butterstick-fpga/butterstick-hardware/documentation/images/800px/butterstick_r1d0_001.jpg

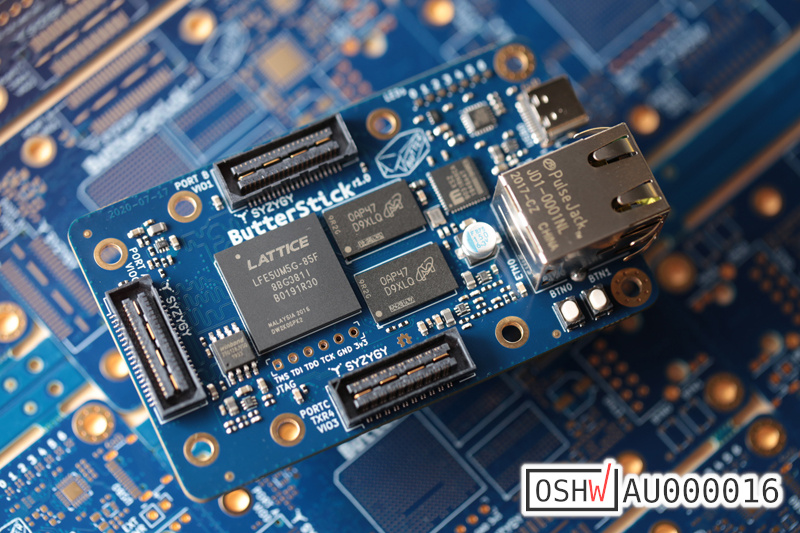
documentation/images/800px/butterstick_r1d0_001.jpg
