butterstick-fpga/butterstick-hardware/documentation/images/butterstick_render_r1d0.png

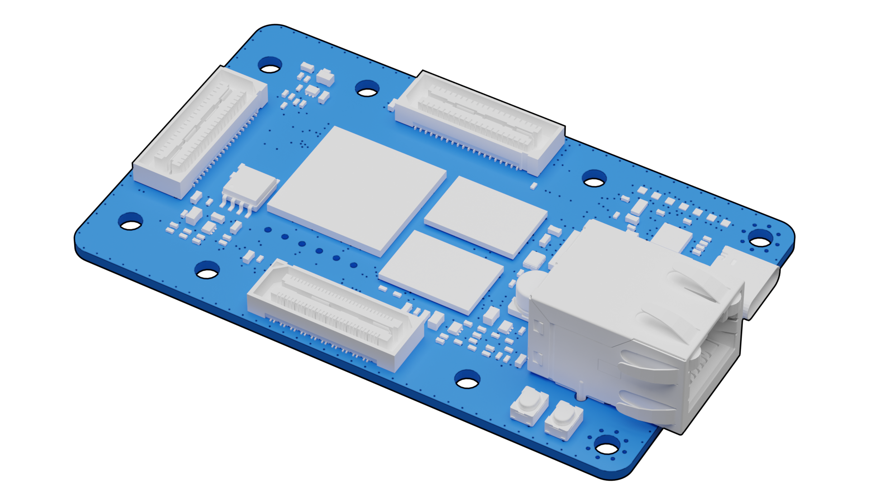
documentation/images/butterstick_render_r1d0.png
