butterstick-fpga/butterstick-hardware/documentation/repository-open-graph-template.png

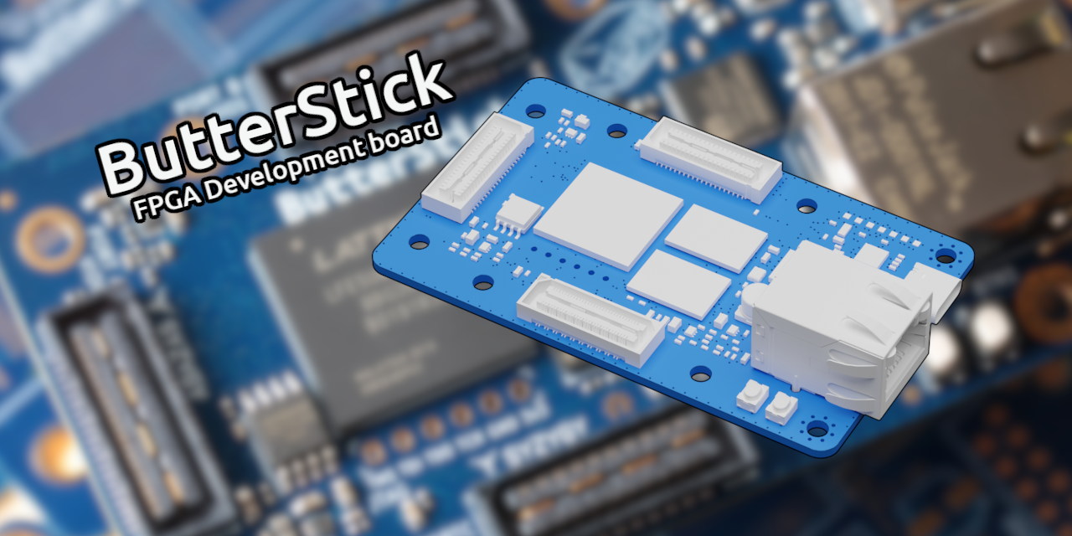
documentation/repository-open-graph-template.png
