butterstick-fpga/butterstick-hardware/hardware/ButterStick_r0.2/output/plot/ButterStick-Back.png

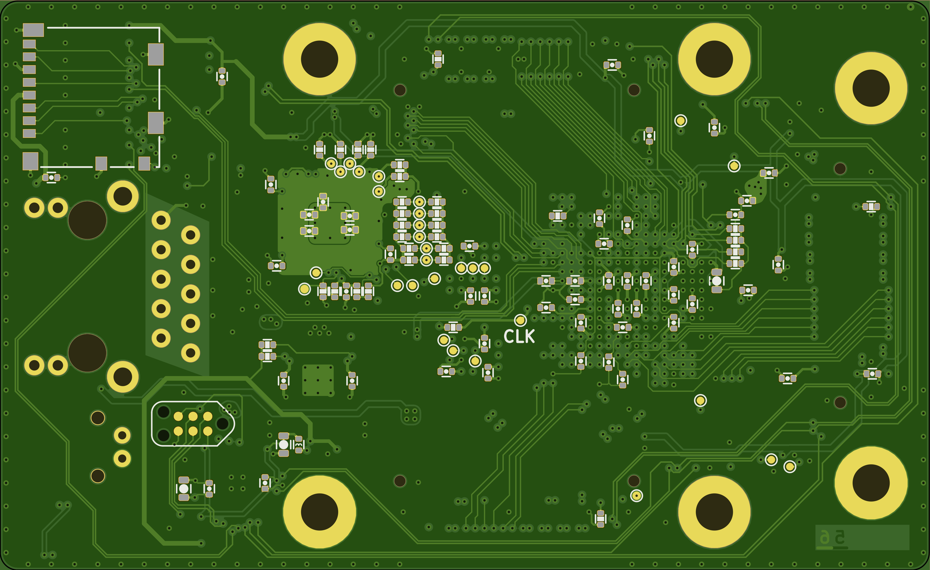
hardware/ButterStick_r0.2/output/plot/ButterStick-Back.png
