butterstick-fpga/butterstick-hardware/hardware/ButterStick_r0.2/output/plot/ButterStick-Front.png

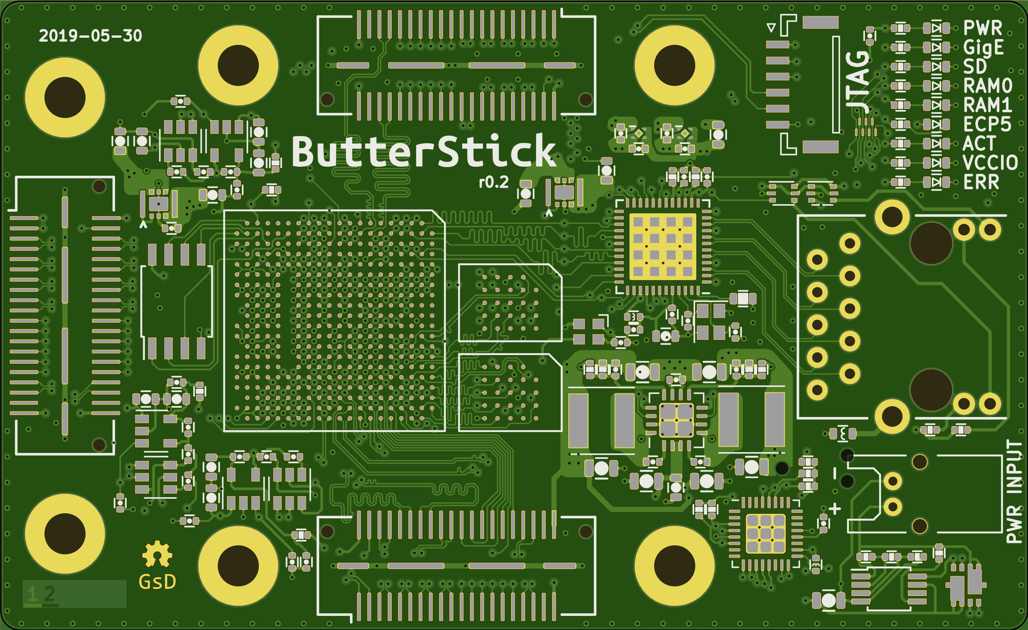
hardware/ButterStick_r0.2/output/plot/ButterStick-Front.png
